viperet/esp8266-wled/images/img1.jpeg

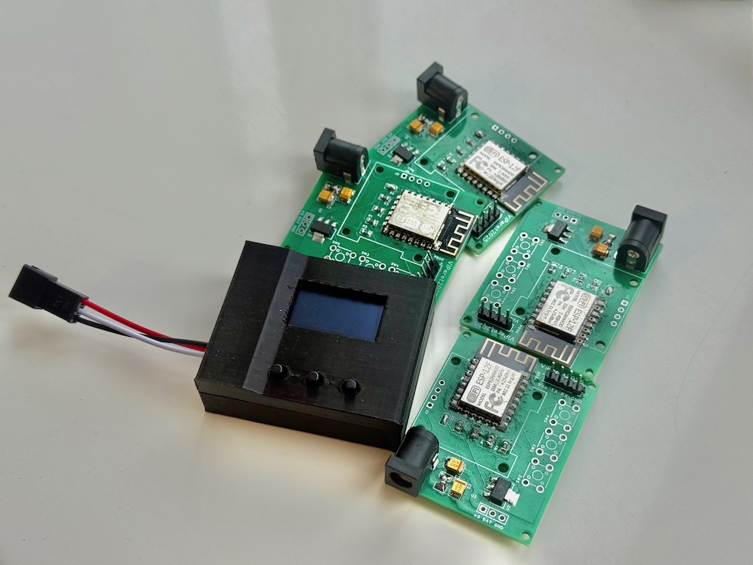
images/img1.jpeg
